74th/relay-switch-usbhub/photos/photo1.jpg

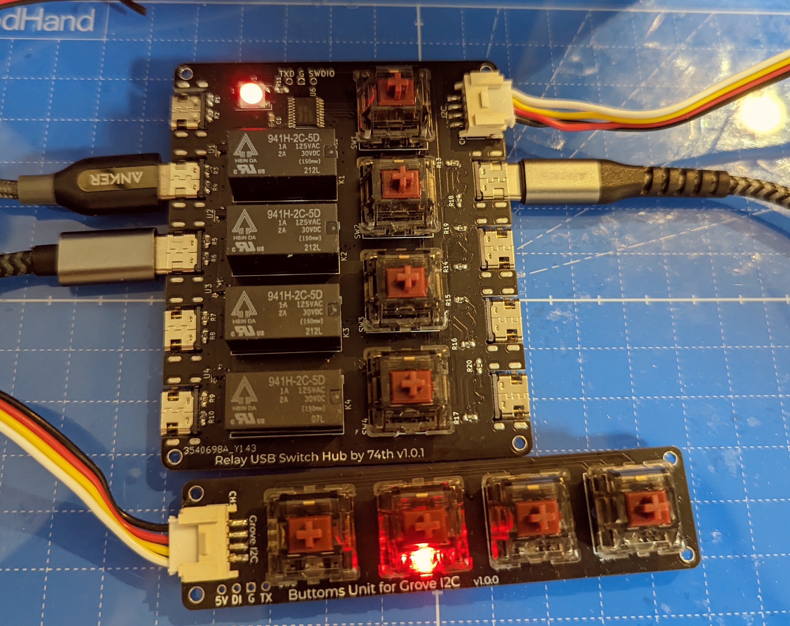
photos/photo1.jpg
